kr3l/sequencer/src/Player.h

#ifndef Player_h
#define Player_h

#include "NotePlayer.h"
#include "TrellisPad.h"

struct Step {
  bool isProgramming;
  float programmedValue; // in autotune mode the note number, otherwise the DAC out voltage 0-3.3V
  bool gateOn;      // true = gate enabled
  uint8_t duty;     // % of step length (0–100)

  bool nowPlaying;
  unsigned long nowPlayingSince;
  bool nowGateHigh;
  bool writtenDac;
};

class Player {
    public:
        Player(TrellisPad *_trellisPad, NotePlayer *_notePlayer, int _numberOfPlayableSteps, int _gatePin, int _triggerPin);
        void stop(void);
        void playSlot(int idx);
        void loop(void);
        bool isPlayingSequence;
        Step steps[16];
        int numberOfPlayableSteps;
        int getPlayingStepNumber(void);
        bool isPlaying(void);
        void updateColorForStep(int idx);
        unsigned long stepDurationMs;
    private:
        TrellisPad *trellisPad;
        NotePlayer *notePlayer;
        int gatePin;
        int triggerPin;
};

#endif
